WolfwithSword/Minibot_Antennae/src/wificonn.py

from pinmgr import PinManager
from utils import Utils, _USE_BLE
from micropython import const
import ure
import errno

try:
    import utime as time
except:
    import time
    
try:
    import usocket as socket
except:
    import socket
    
import wifimgr
from network import hostname

_HTTP_OK = const('HTTP/1.1 200 OK\n')
_URL_RE = const("(?:GET|POST) /(.*?)(?:\\?.*?)? HTTP")
_QUERY_RE = const("(?:GET|POST) /(.*?) HTTP")
_METHOD_RE = const("^(GET|POST|PATCH|DELETE) /")
_PLAIN_TXT = const('Content-Type: text/plain\n')

def get_url(request):
    if "HTTP" not in request:
        return '', '', ''
    query_param = ''
    try:
        url = ure.search(_URL_RE, request).group(1).decode("utf-8").rstrip("/")
        method = ure.search(_METHOD_RE, request).group(1).decode("utf-8")
        query_param = ure.search(_QUERY_RE, request).group(1).decode("utf-8")
    except Exception:
        url = ure.search(_URL_RE, request).group(1).rstrip("/")
        method = ure.search(_METHOD_RE, request).group(1)
        query_param = ure.search(_QUERY_RE, request).group(1)
    url = "/" + url
    query_param = "/" + query_param
    return url.strip(), method.strip(), query_param.strip()

_data = {}

class WiFiConn():
    
    def __init__(self, pins: PinManager, _utils: Utils):
        self.pins = pins
        self.utils = _utils

    def req_handler(self, cs):
        try:
            req = cs.read()
            if req:
                url, method, query_param = get_url(req)
                if method == 'GET':
                    if url in ['/', '/data']:
                        _data['battery_voltage'] = self.pins.get_battery_voltage()
                        #_data['battery_adc_raw'] = self.pins.battery_pin.read()
                        _data['uptime_s'] = self.utils.get_elapsed_time()
                        rep = _data
                        cs.send(_HTTP_OK)
                        cs.send('Content-Type: application/json\n')
                    elif url.startswith('/restart'):
                        cs.send(_HTTP_OK)
                        cs.send(_PLAIN_TXT)
                        rep = 'Restarting...'
                        cs.send('Connection: close\n\n')
                        cs.sendall(rep)
                        time.sleep(1)
                        cs.close()
                        self.utils.restart()
                        return
                    elif url.startswith('/leds'):
                        if url == '/leds/right/off':
                            self.pins.stop_right_light()
                        elif url == '/leds/right/on':
                            self.pins.start_right_light()
                        elif url == '/leds/left/off':
                            self.pins.stop_left_light()
                        elif url == '/leds/left/on':
                            self.pins.start_left_light()
                        elif url == '/leds/sync/off':
                            self.pins.stop_sync_lights()
                        elif url == '/leds/sync/on':
                            self.pins.start_sync_lights()
                        elif query_param.startswith('/leds?'):
                            delay = None
                            steps = None
                            valid_req = False
                            if 'delay=' in query_param:
                                val = query_param.split("delay=")[1]
                                if "&" in val:
                                    val = val.split("&")[0]
                                try:
                                    if val == "default":
                                        delay = 0.03
                                    else:
                                        delay = float(val)
                                except:
                                    delay = None
                                if delay is not None:
                                    valid_req = True
                            if 'steps=' in query_param:
                                val = query_param.split("steps=")[1]
                                if "&" in val:
                                    val = val.split("&")[0]
                                try:
                                    if val == "default":
                                        steps = 32
                                    else:
                                        steps = int(val)
                                except:
                                    steps = None
                                if steps is not None:
                                    valid_req = True
                            if not valid_req:
                                rep = 'Malformed Request'
                                cs.send('HTTP/1.1 400 MALFORMED REQUEST\n')
                                cs.send(_PLAIN_TXT)
                                cs.send('Connection: close\n\n')
                                cs.sendall(rep)
                                cs.close()
                                return
                            else:
                                if delay is not None:
                                    self.pins.set_delay(delay)
                                if steps is not None:
                                    self.pins.set_steps(steps)
                            
                        cs.send(_HTTP_OK)
                        cs.send(_PLAIN_TXT)
                        rep = 'OK'
                    elif url.startswith('/mode/'):
                        cs.send(_HTTP_OK)
                        cs.send(_PLAIN_TXT)
                        
                        # Mode 0 will be irrecoverable without reflashing
                        if url == '/mode/1':
                            # Already in Mode 1 because this is wifi
                            rep = 'Already in WiFi Mode'
                        elif url == '/mode/2':
                            rep = 'Switching to BLE...'
                            cs.send('Connection: close\n\n')
                            cs.sendall(rep)
                            time.sleep(2)
                            cs.close()
                            self.utils.switch_mode(_USE_BLE)
                            return
                    else:
                        rep = 'Not Found'
                        cs.send('HTTP/1.1 404 NOT FOUND\n')
                        cs.send(_PLAIN_TXT)
                else:
                    rep = 'Not Found'
                    cs.send('HTTP/1.1 404 NOT FOUND\n')
                    cs.send(_PLAIN_TXT)
            
                cs.send('Connection: close\n\n')
                cs.sendall(str(rep).replace("'", '"'))
                #print(rep)
            else:
                print('Client close connection')
        except Exception as e:
            print('Err:', e)
        cs.close()

    def cln_handler(self, srv):
        cs = None
        try:
            cs,ca = srv.accept()
            cs.setblocking(False)
            #cs.settimeout(5)
            cs.setsockopt(socket.SOL_SOCKET, 20, self.req_handler)
        except Exception as e:
            print("Exception in cln_handler: ", e)
            if cs:
                cs.close()
                
        
    def start_socket(self, ignore_error=False):
        try: 
            port = self.utils.config.get('wifi', {}).get('port', 8080)
            addr = socket.getaddrinfo('0.0.0.0', port)[0][-1]
            sock = socket.socket(socket.AF_INET, socket.SOCK_STREAM)
            sock.setsockopt(socket.SOL_SOCKET, socket.SO_REUSEADDR, 1)
            sock.bind(addr)
            sock.listen(self.utils.config.get('wifi', {}).get('max_connections', 2)) # Max number of clients
            #srv.settimeout(5)
            sock.setblocking(False)
            sock.setsockopt(socket.SOL_SOCKET, 20, self.cln_handler)
            return sock
        except OSError as e:
            if not ignore_error:
                print("Restarting due to socket error: ", e)
                self.utils.restart()
                
    def start(self):
        wlan = wifimgr.get_connection()
        if wlan is None:
            print("Unable to initialize network connection")
            while True:
                pass
        print("IP is: "+wlan.ifconfig()[0])
        print("Hostname is: " + hostname())
        _sock = self.start_socket()
        return _sock
    
    
    def run(self):
        print("Running WiFi")
        _sock = self.start()
        while True:
            time.sleep(10)
            if _sock:
                try:
                    # Test socket is still up
                    _sock.sendall("test")
                except OSError as oe:
                    if oe.args[0] != errno.EAGAIN:
                        _sock = None
                        gc.collect()
                        print("Restarting Socket...")
                        _sock = self.start_socket(ignore_error=True)
                except Exception as e1:
                    try:
                        _sock.close()
                    except Exception as e2:
                        pass
                    _sock = None
                    gc.collect()
                    print("Restarting Socket...")
                    _sock = self.start_socket(ignore_error=True)
            pass
